brianhtam/CE122_bridge_design_optimization/Design Dwg/pdfs/Framing Plan 03092017.pdf

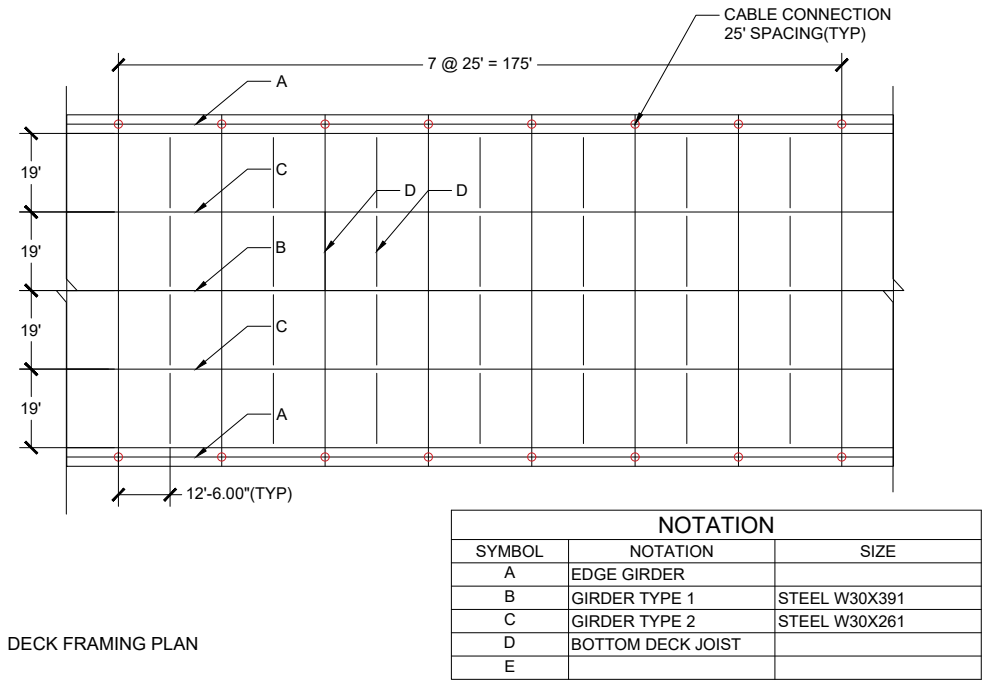
[picture p34: page 1]
CABLE CONNECTION 25' SPACING(TYP) 19' 19' 19' 19'; 12'-6.00"(TYP) DECK FRAMING PLAN; NOTATION SYMBOL; NOTATION; SIZE A; EDGE GIRDER B; GIRDER TYPE 1; STEEL W30X391 C; GIRDER TYPE 2; STEEL W30X261 D; BOTTOM DECK JOIST E CABCA
