brianhtam/CE122_bridge_design_optimization/Design Dwg/pdfs/Framing Plan 03102017.pdf

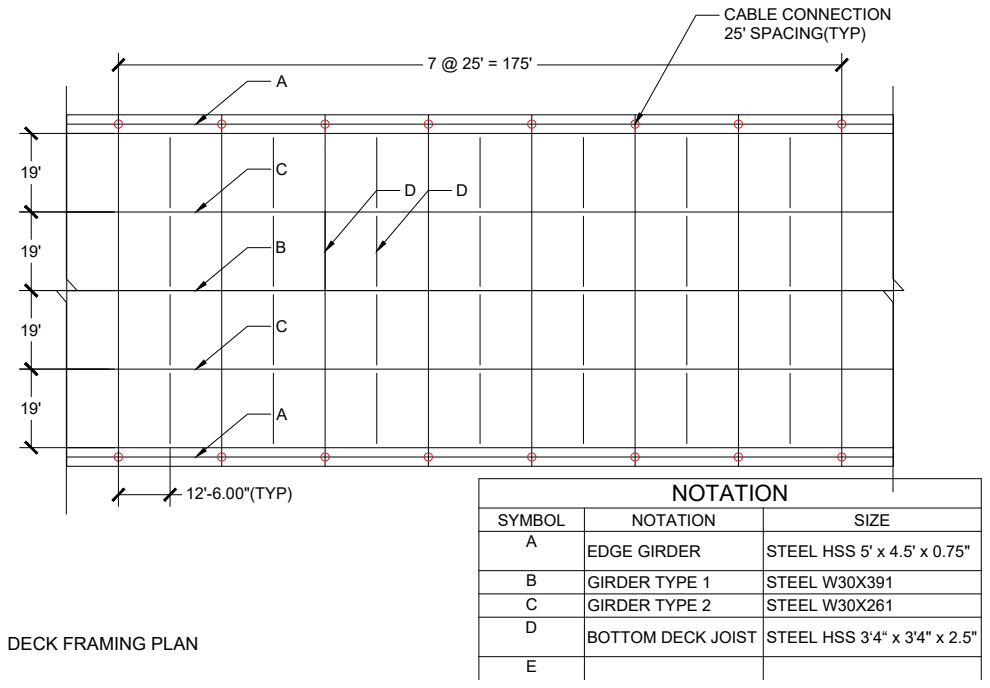
[picture p35: page 1]
CABLE CONNECTION 25' SPACING(TYP) 19' 19' 19' 19'; 12'-6.00"(TYP) DECK FRAMING PLAN; NOTATION SYMBOL; NOTATION; SIZE A; EDGE GIRDER; STEEL HSS 5' x 4.5' x 0.75" B; GIRDER TYPE 1; STEEL W30X391 C; GIRDER TYPE 2; STEEL W30X261 D; BOTTOM DECK JOIST; STEEL HSS 3‘4“ x 3'4" x 2.5" E CABCA
