brianhtam/CE122_bridge_design_optimization/Design Dwg/pdfs/Preliminary-Elevation.pdf

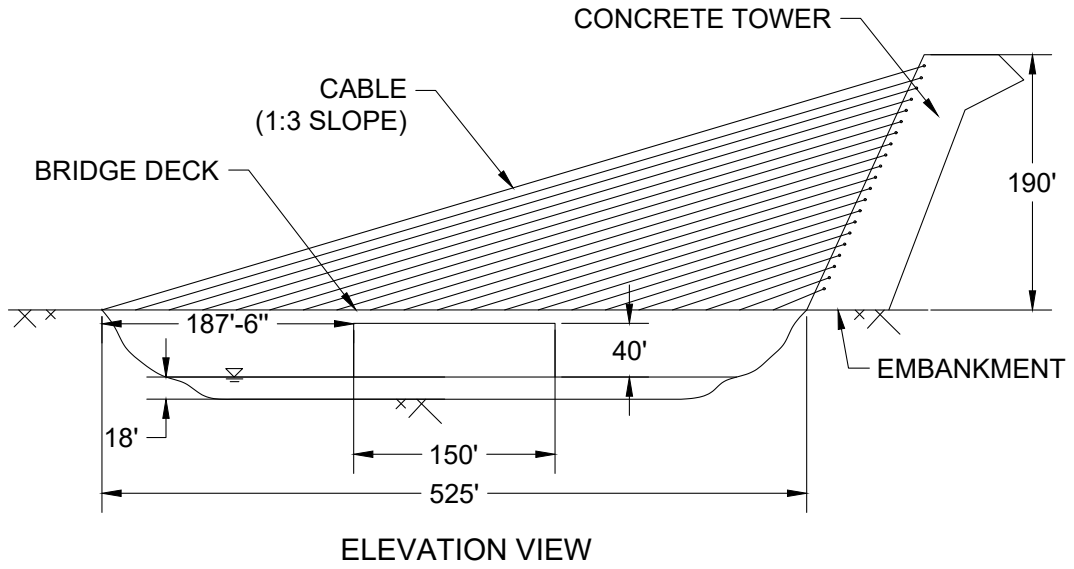
[picture p36: page 1]
EMBANKMENT CABLE (1:3 SLOPE); CONCRETE TOWER BRIDGE DECK; ELEVATION VIEW
