brianhtam/CE122_bridge_design_optimization/PDF/Use/final fram.pdf

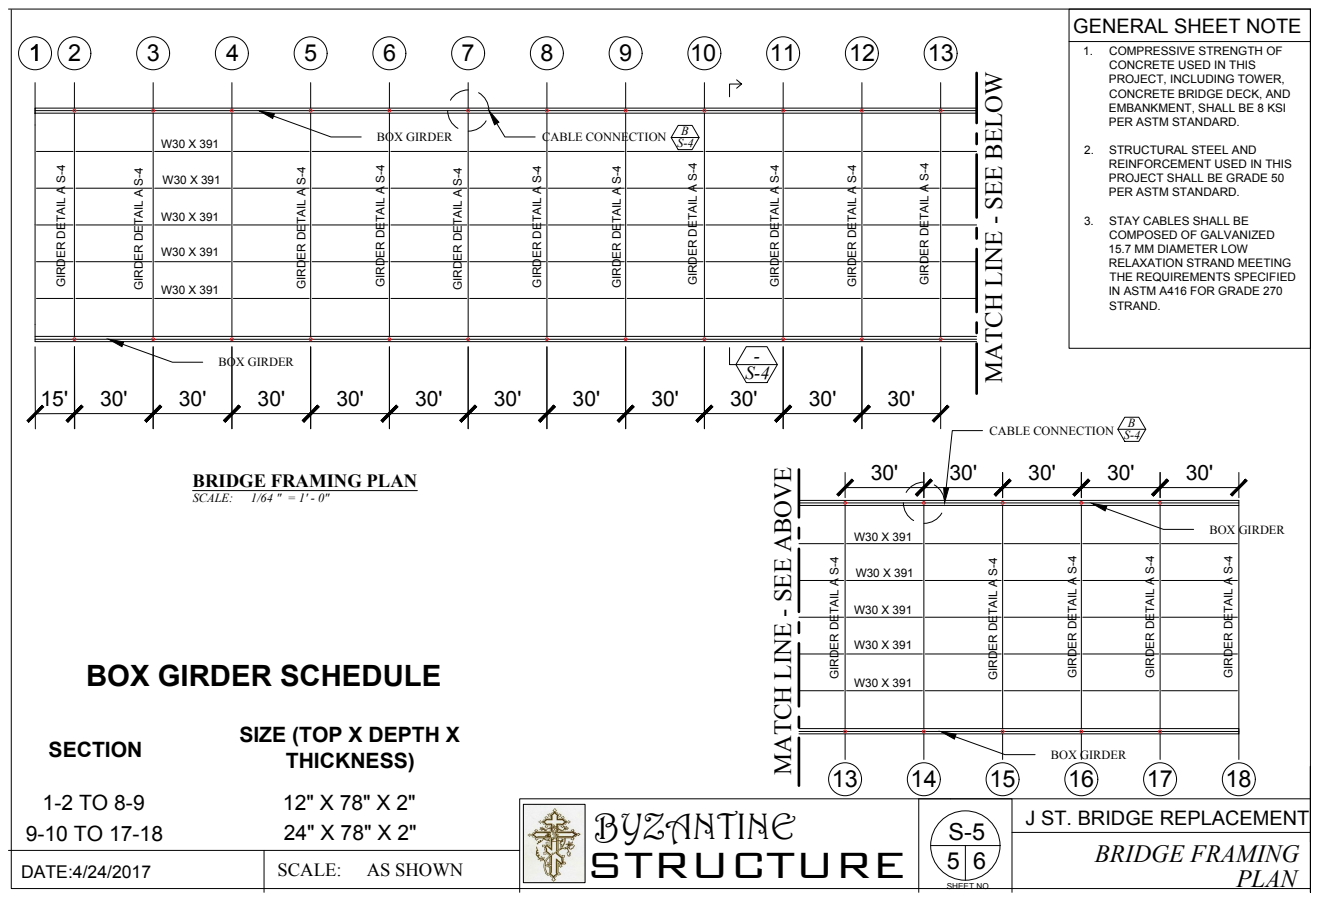
[picture p37: page 1]
BOX GIRDER; BRIDGE FRAMING STRUCTURE; PLAN BYZANTINE; J ST. BRIDGE REPLACEMENT SHEET NO. 5; GENERAL SHEET NOTE 1.; COMPRESSIVE STRENGTH OF CONCRETE USED IN THIS PROJECT, INCLUDING TOWER, CONCRETE BRIDGE DECK, AND EMBANKMENT, SHALL BE 8 KSI PER ASTM STANDARD. 2.; STRUCTURAL STEEL AND REINFORCEMENT USED IN THIS PROJECT SHALL BE GRADE 50 PER ASTM STANDARD. 3.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

MATCH LINE - SEE BELOW

GIRDER DETAIL A S-4 BOX GIRDER BOX GIRDER BOX GIRDER CABLE CONNECTION CABLE CONNECTION BOX GIRDER SCHEDULE SECTION SIZE (TOP X DEPTH X THICKNESS) 1-2 TO 8-9 12" X 78" X 2" 9-10 TO 17-18 24" X 78" X 2" BRIDGE FRAMING PLAN SCALE: 1/64 " = 1' - 0"

MATCH LINE - SEE ABOVE
