brianhtam/CE122_bridge_design_optimization/Design Dwg/pdfs/Byzantine - Preliminary-Deck Cross Section.pdf

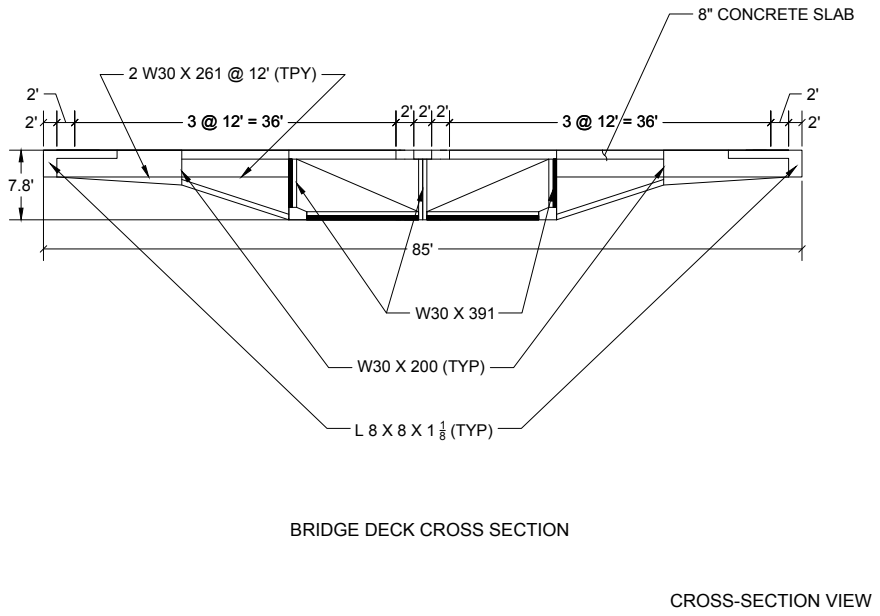
[picture p39: page 1]
CROSS-SECTION VIEW BRIDGE DECK CROSS SECTION 85' 7.8'; 8" CONCRETE SLAB 3 @ 12' = 36'; 2' 2' 2 W30 X 261 @ 12' (TPY); L 8 X 8 X 1 18 (TYP) W30 X 200 (TYP) W30 X 391
