brianhtam/CE122_bridge_design_optimization/Design Dwg/pdfs/Cross Section 03092017.pdf

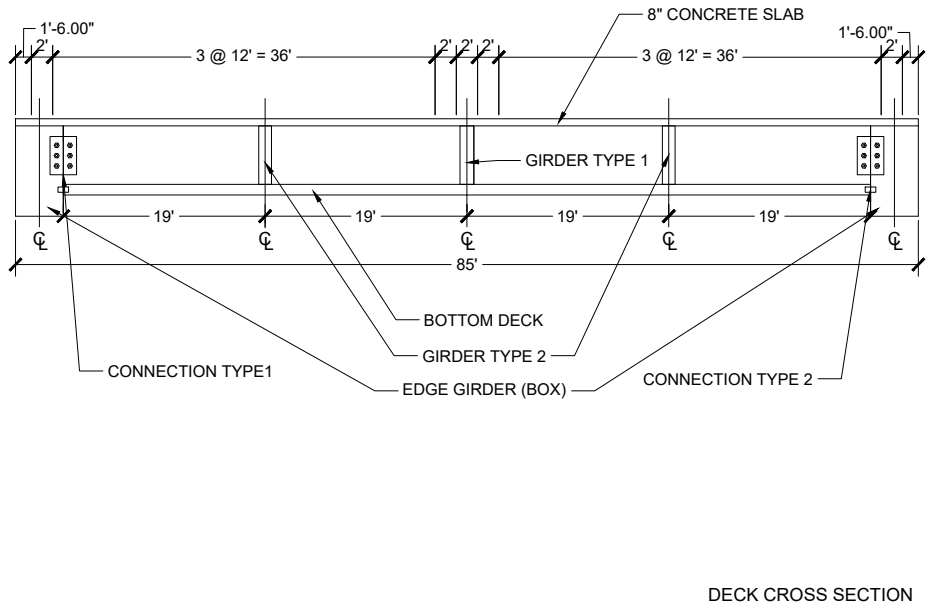
[picture p40: page 1]
DECK CROSS SECTION 1'-6.00" 2'; CL 8" CONCRETE SLAB EDGE GIRDER (BOX) GIRDER TYPE 2 GIRDER TYPE 1 CONNECTION TYPE1; CONNECTION TYPE 2 BOTTOM DECK 19'
