brianhtam/CE122_bridge_design_optimization/Design Dwg/pdfs/Top View 03102017.pdf

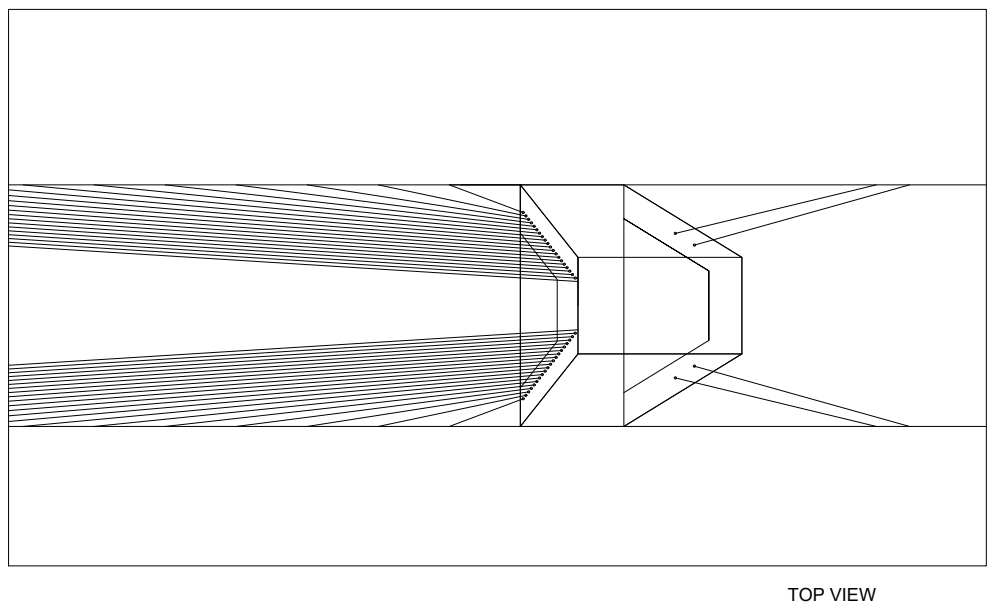
[picture p41: page 1]
TOP VIEW
