brianhtam/CE122_bridge_design_optimization/Design Dwg/New New New/OK/Towert.pdf

TOWER CROSS SECTION VIEW 85'; CONCRETE F'c = 4 ksi Fy = 60 ksi
