brianhtam/CE122_bridge_design_optimization/PDF/Use/s-1.pdf

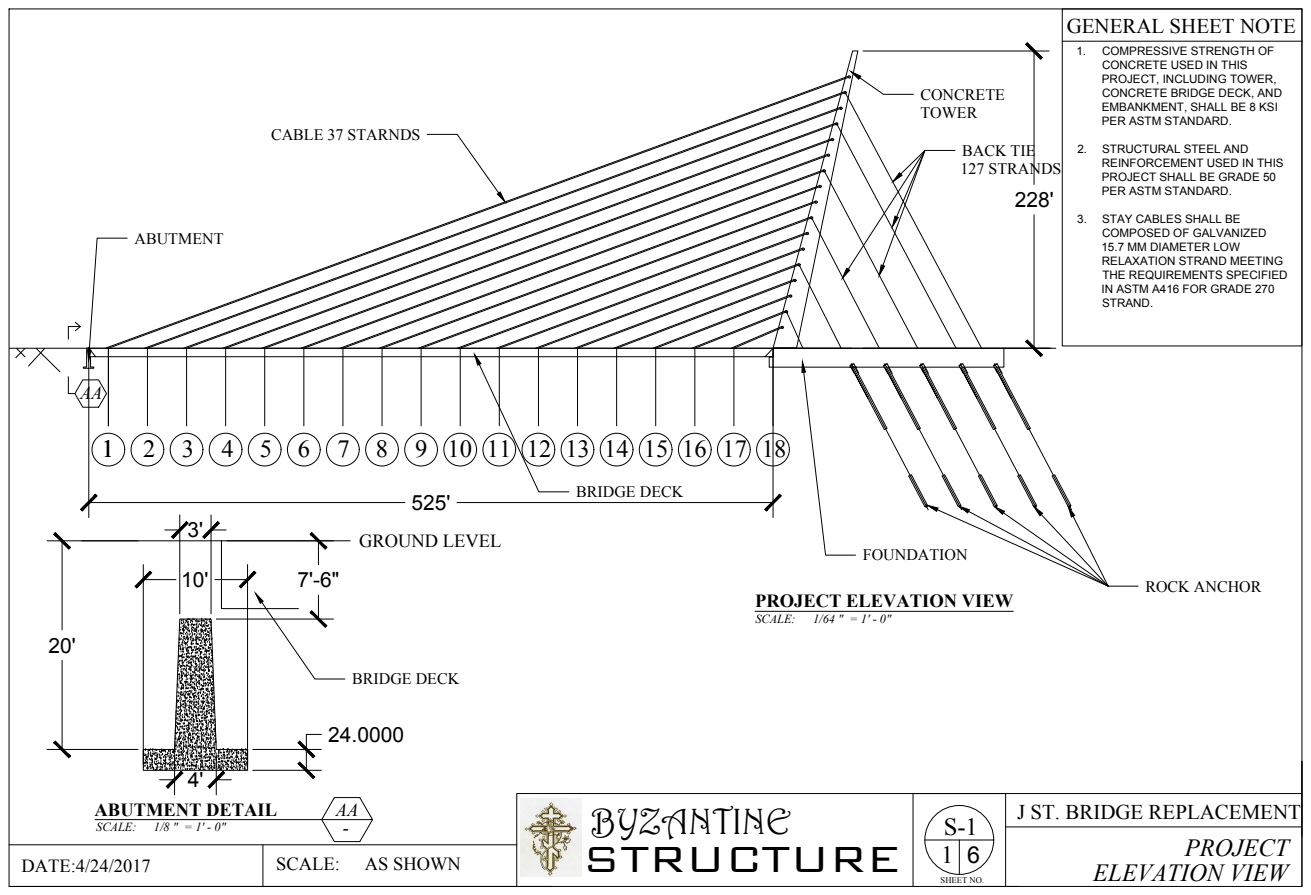
[picture p42: page 1]
PROJECT STRUCTURE; ELEVATION VIEW BYZANTINE; J ST. BRIDGE REPLACEMENT SHEET NO. 1; 6 S-1 DATE:4/24/2017; GENERAL SHEET NOTE 1.; COMPRESSIVE STRENGTH OF CONCRETE USED IN THIS PROJECT, INCLUDING TOWER, CONCRETE BRIDGE DECK, AND EMBANKMENT, SHALL BE 8 KSI PER ASTM STANDARD. 2.; STRUCTURAL STEEL AND REINFORCEMENT USED IN THIS PROJECT SHALL BE GRADE 50 PER ASTM STANDARD. 3.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
