brianhtam/CE122_bridge_design_optimization/PDF/Use/S-3.pdf

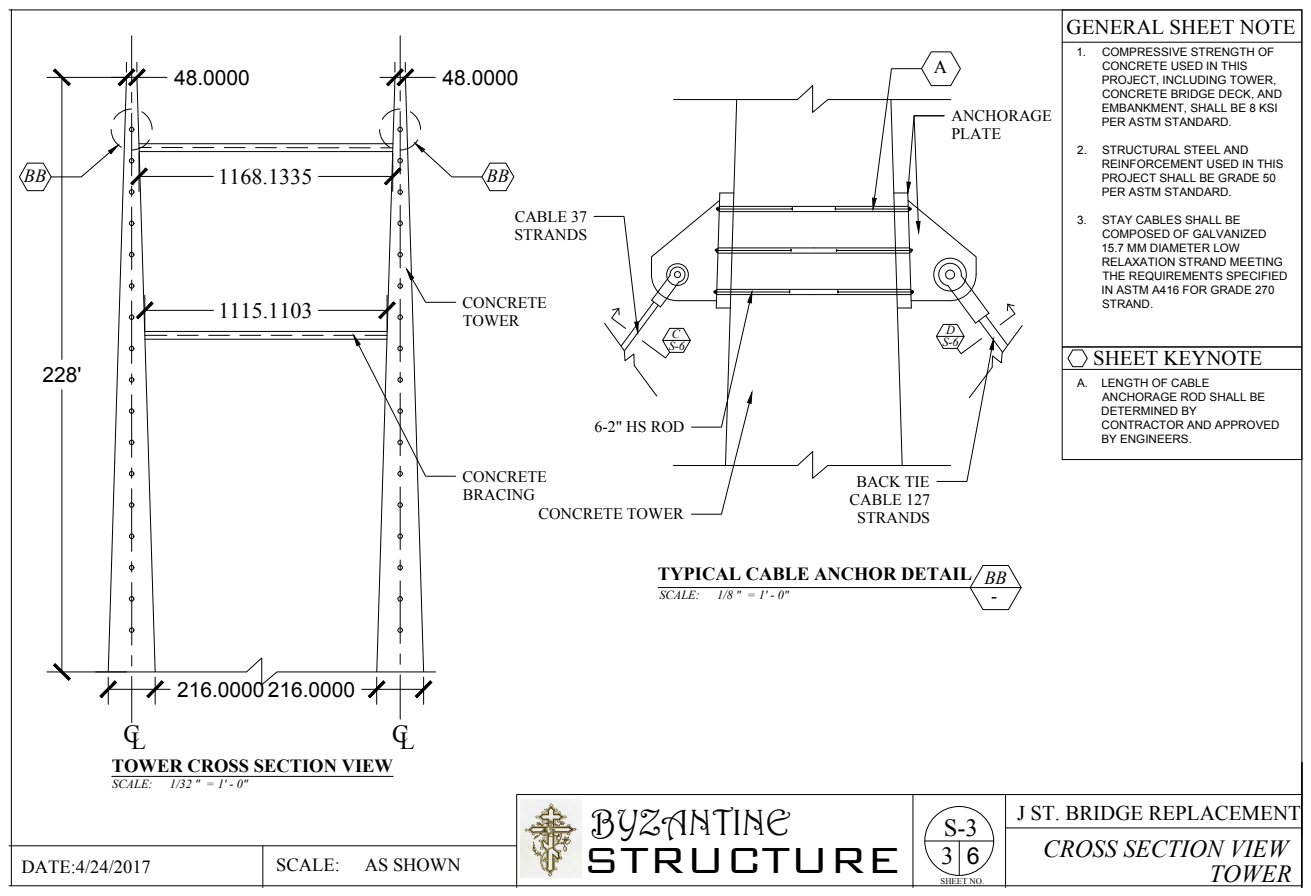
[picture p43: page 1]
CROSS SECTION VIEW STRUCTURE; TOWER BYZANTINE; J ST. BRIDGE REPLACEMENT SHEET NO. 3; GENERAL SHEET NOTE SHEET KEYNOTE 1.; COMPRESSIVE STRENGTH OF CONCRETE USED IN THIS PROJECT, INCLUDING TOWER, CONCRETE BRIDGE DECK, AND EMBANKMENT, SHALL BE 8 KSI PER ASTM STANDARD. 2.; STRUCTURAL STEEL AND REINFORCEMENT USED IN THIS PROJECT SHALL BE GRADE 50 PER ASTM STANDARD. 3.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
