brianhtam/CE122_bridge_design_optimization/Design Dwg/Archive/Byzantine-Preliminary-Cross-Section.pdf

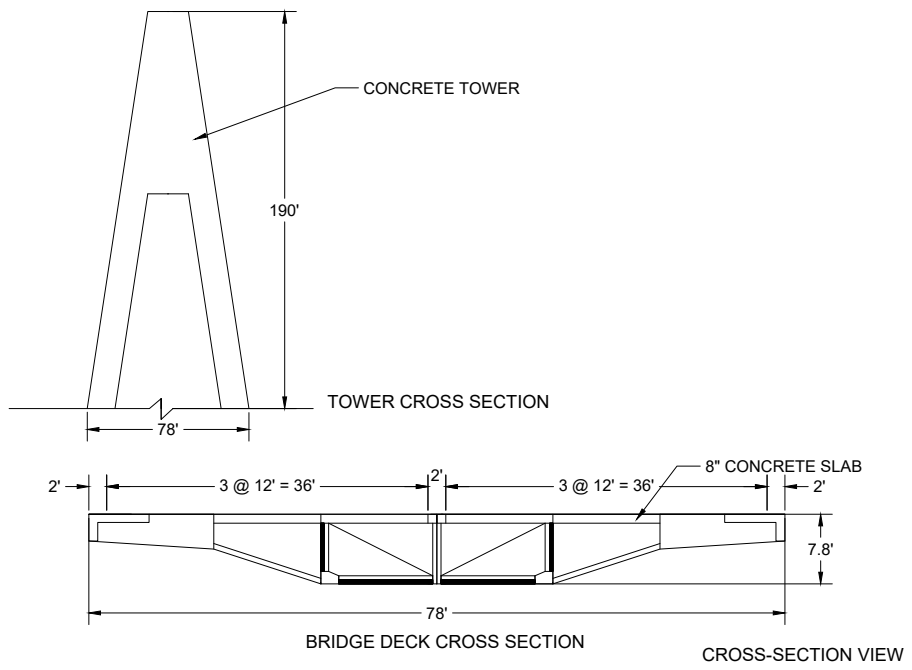
[picture p44: page 1]
CROSS-SECTION VIEW 78'; 190' BRIDGE DECK CROSS SECTION TOWER CROSS SECTION 78'; 7.8' CONCRETE TOWER; 8" CONCRETE SLAB 2'
